facunava/Tesis_2021/01_hardware/v0/v0.sch

## KiCad design 01_hardware/v0/v0.sch (2021-06-29)

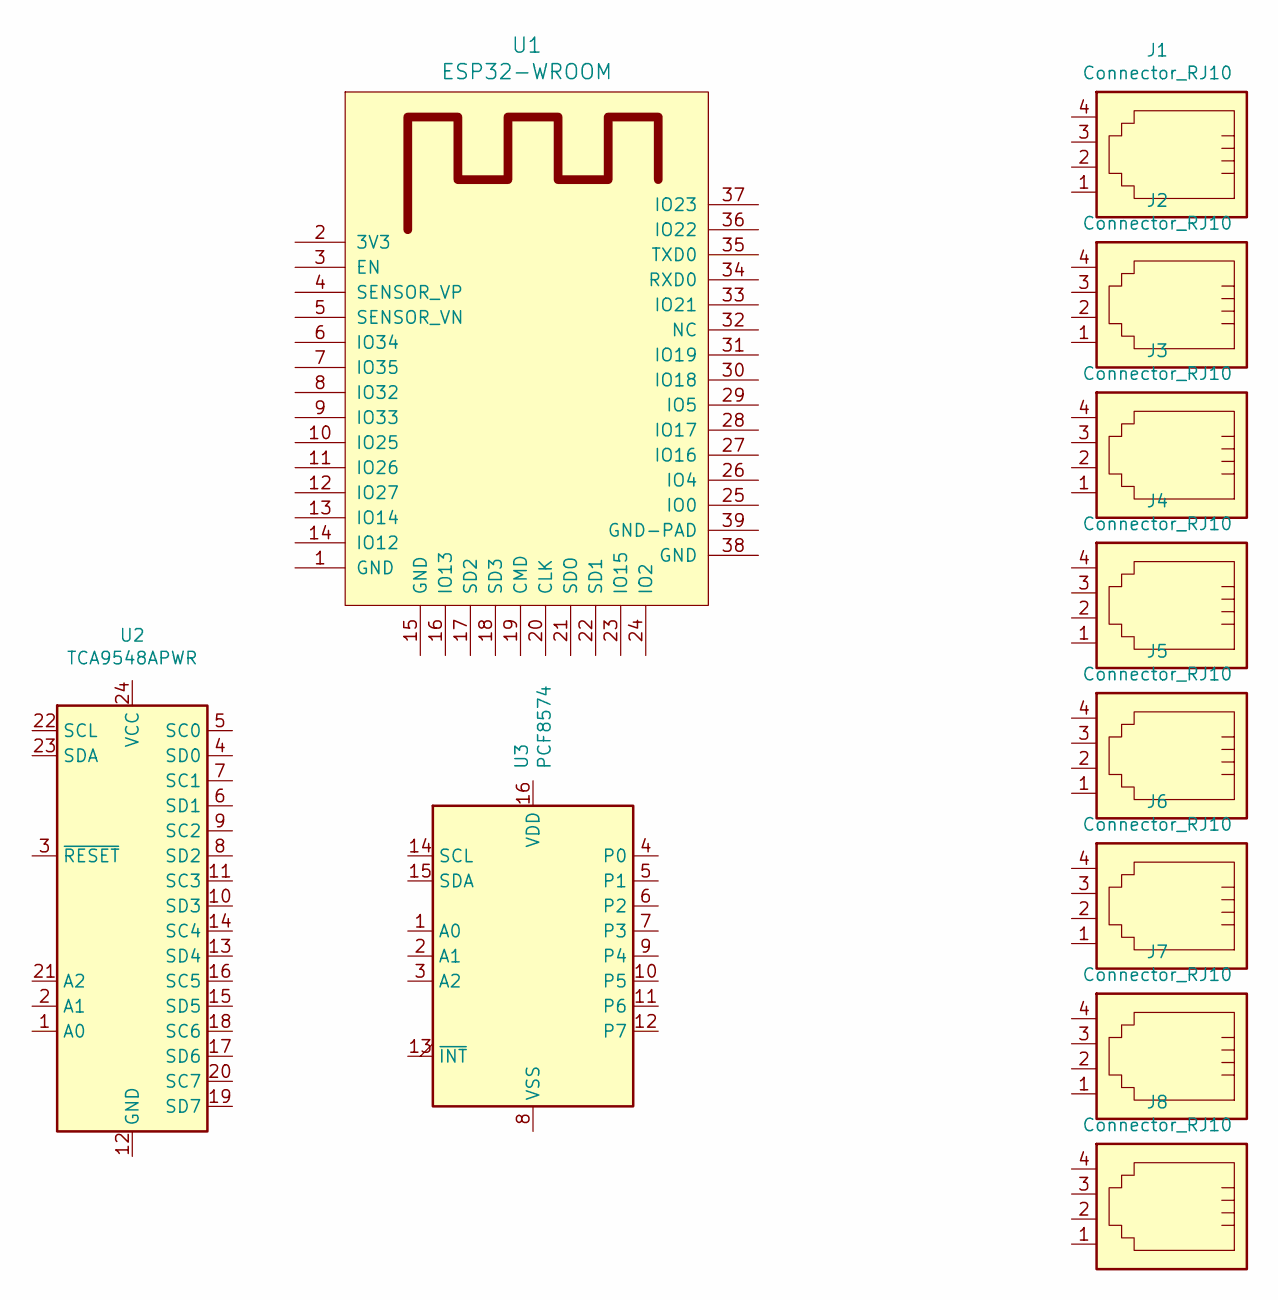
[picture p14: schematic v0.sch]

Parts:
J1, J2, J3, J4, J5, J6, J7, J8: Connector_RJ10; 4P4C_narrow
U1: ESP32-WROOM
U2: TCA9548APWR; TSSOP-24_4.4x7.8mm_P0.65mm
U3: PCF8574; SOIC-16W_7.5x10.3mm_P1.27mm
